schuyler4/Basic_Diff_Probe/simulation/diff_stage.asc

R1: res; 10k
R2: res; 10k
R3: res; 10k
R4: res; 10k
R5: res; 100k
R6: res; 100k
R7: res; 900k
R8: res; 900k
U1: UniversalOpAmp
U2: UniversalOpAmp
U3: UniversalOpAmp
V1: voltage; 4.5V
V2: voltage; 4.5V
V3: voltage; 4.5V
V4: voltage; 25V
V5: voltage; 4.5V
V6: voltage; 4.5V
V7: voltage; 4.5V
V8: voltage; 5
V9: voltage; 1.35mV
V10: voltage; 1.35mV
V11: voltage; 1.35mV
Named nets: 0
.tran 10ms
